udu3324/mpe32board-midi/cart/jlcpcb-mpe32board grandtotal.png

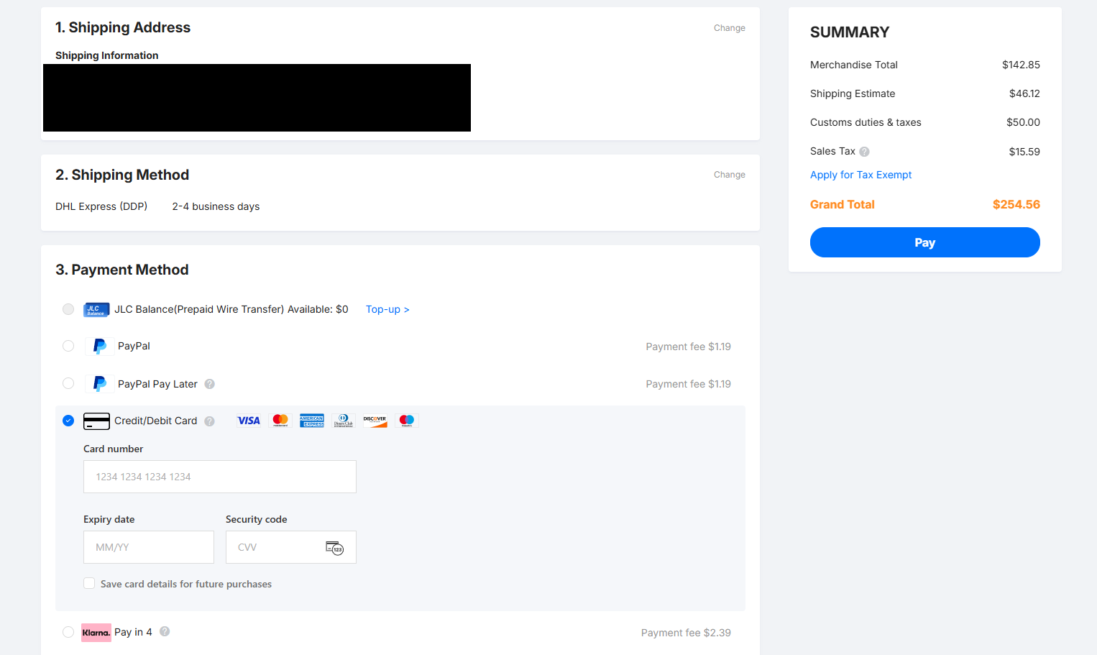
cart/jlcpcb-mpe32board grandtotal.png
