udu3324/mpe32board-midi/cart/jlcpcb-mpe32sensor grandtotal.png

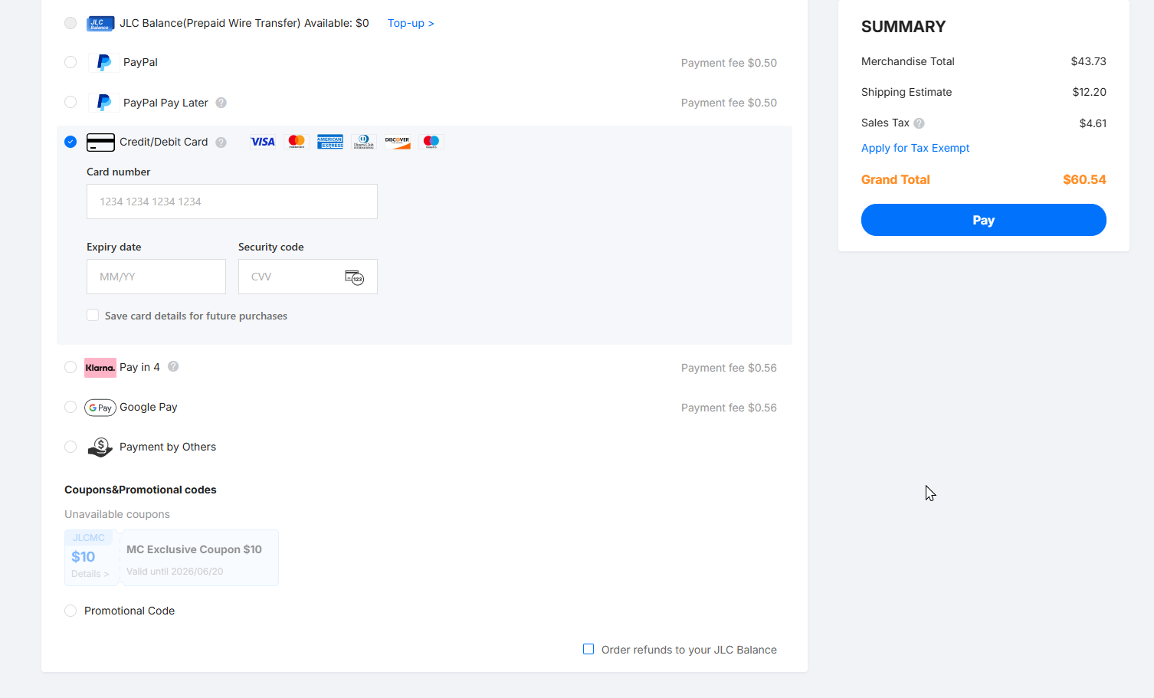
cart/jlcpcb-mpe32sensor grandtotal.png
