udu3324/mpe32board-midi/cart/jlcpcb-mpe32sensor price breakdown.png

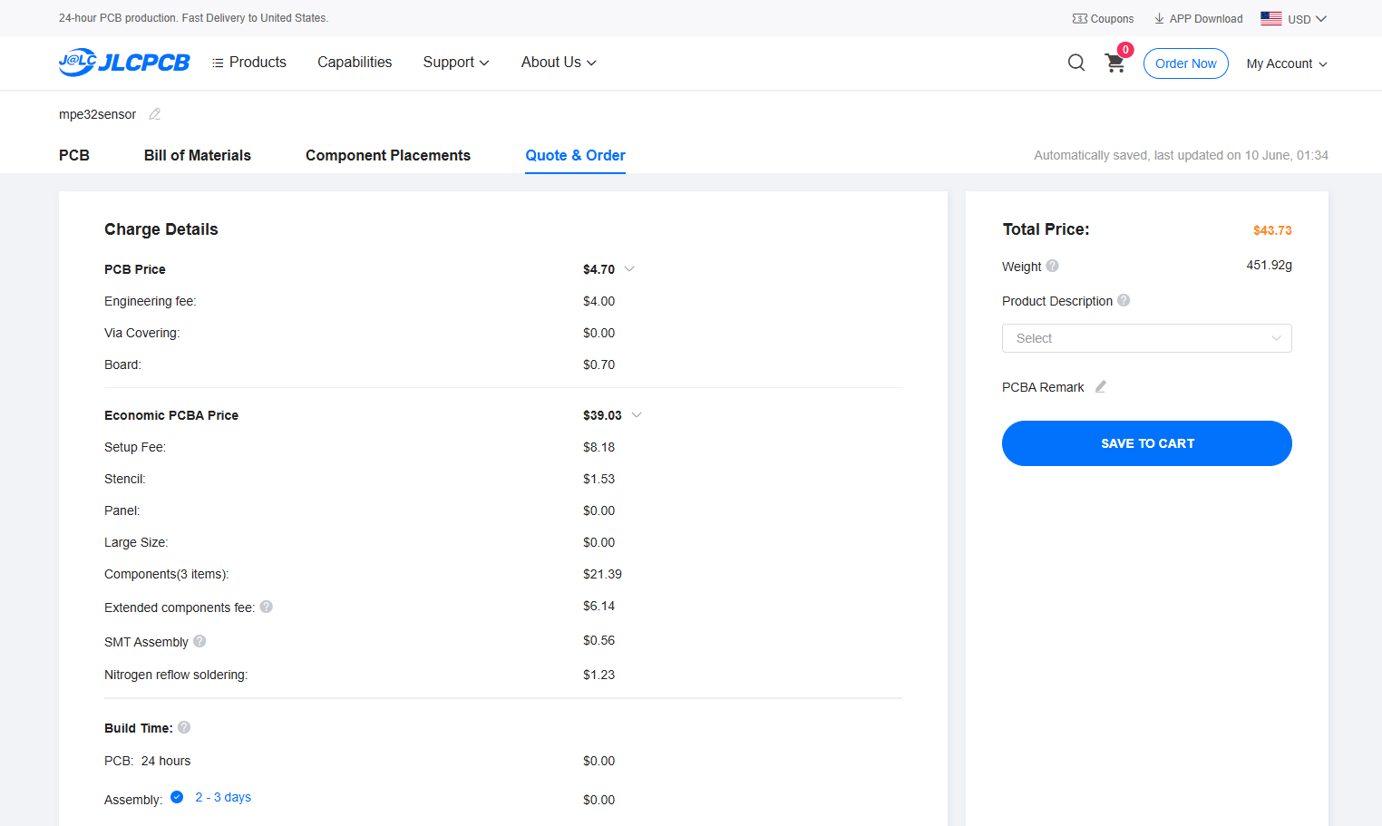
cart/jlcpcb-mpe32sensor price breakdown.png
