udu3324/mpe32board-midi/cart/jlcpcb-mpe32sensor subtotal 2.png

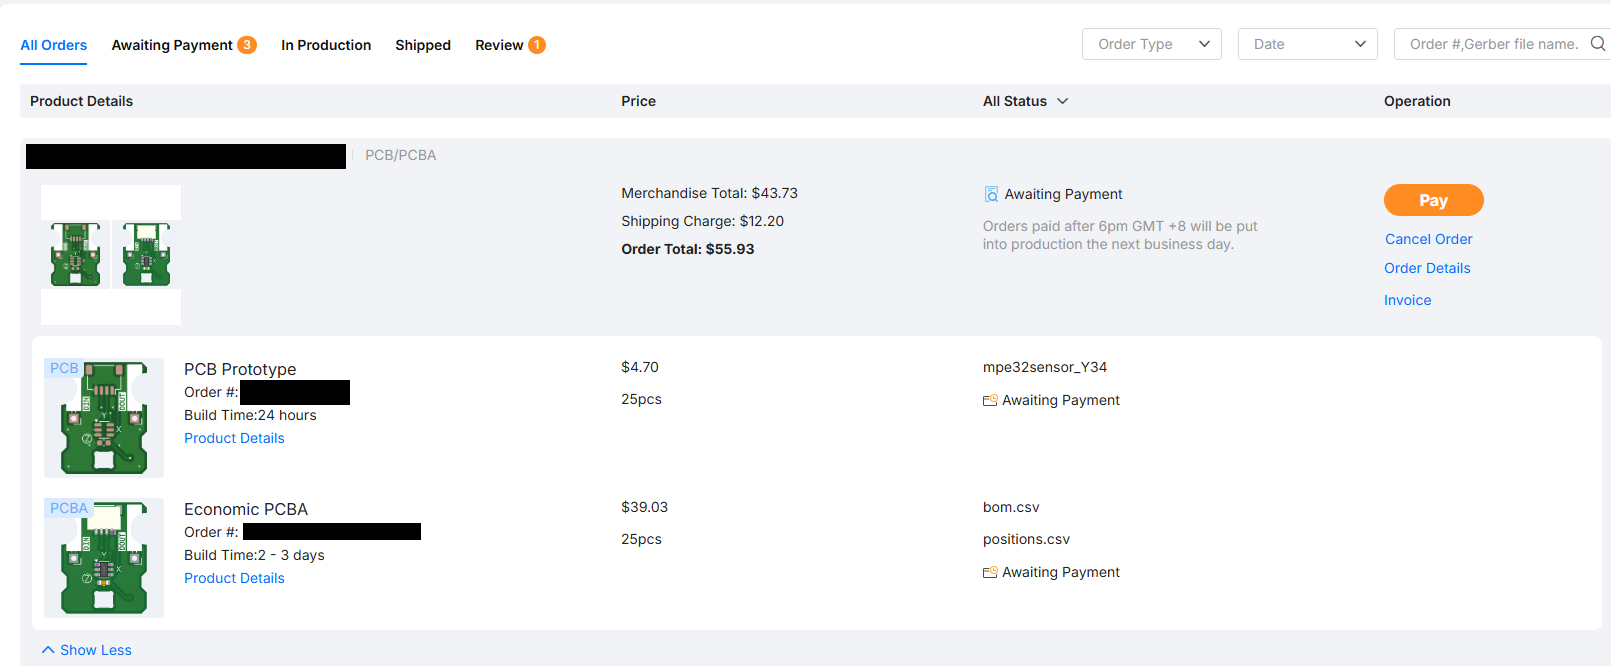
cart/jlcpcb-mpe32sensor subtotal 2.png
