udu3324/mpe32board-midi/pcb/mpe32board-F_Silkscreen.png

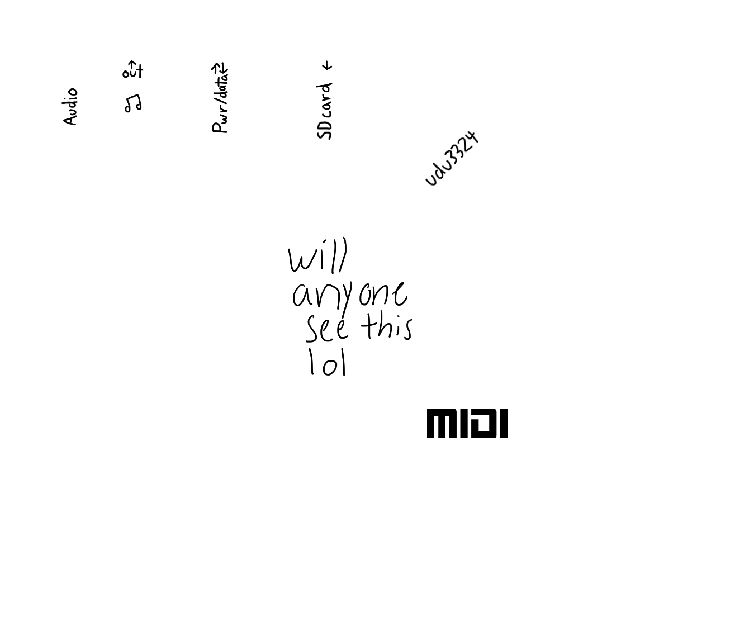
pcb/mpe32board-F_Silkscreen.png
