udu3324/mpe32board-midi/pcb/misc components/472192001.stp

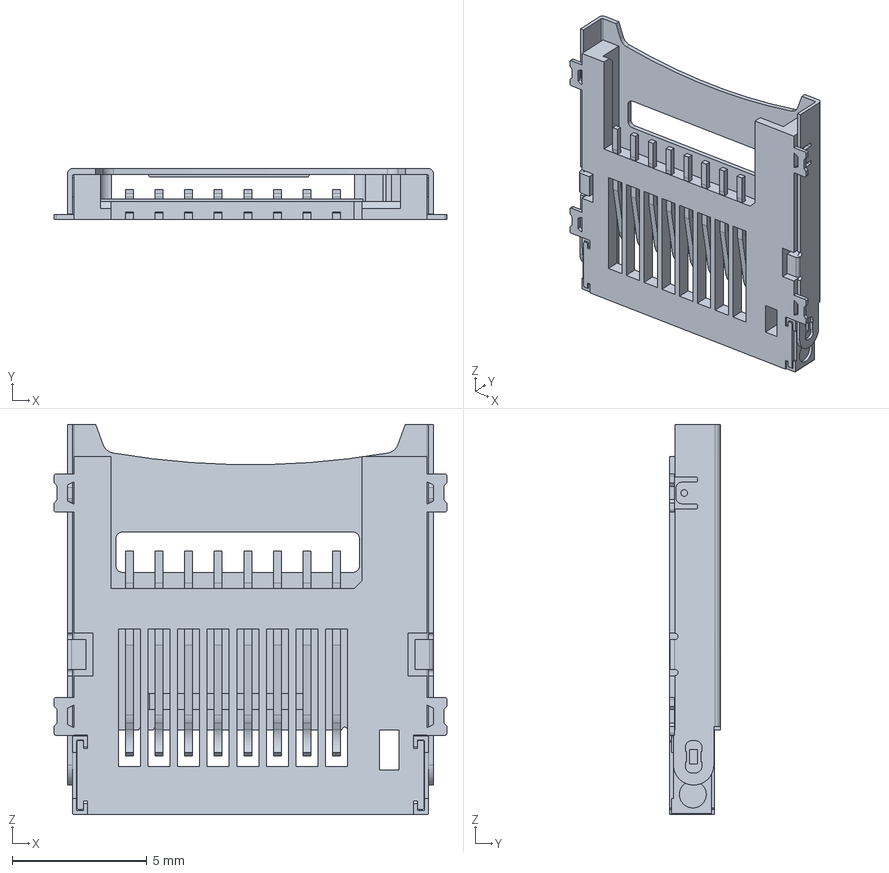
[picture p42: CAD file, 2026-04-25]
pcb/misc components/472192001.stp
14.6 x 1.90 x 14.5 mm
